InputBlackBoxOutput/NETHER/modules/HID module/firmware/src/connections.h

// AUX GPIO: Added for future extension and not used
// The ADC channel connected to pin 35 can be used to check LiPo battery voltage

#ifndef CONNECTIONS_H
#define CONNECTIONS_H

#define LED_S   16
#define LED_P   17

#define LED     22

#define AUX_1   23
#define AUX_2   25
#define AUX_3   26
#define AUX_4   27
#define AUX_5   32  // ADC
#define AUX_6   33  // ADC
#define AUX_7   34  // ADC
#define AUX_8   35  // ADC

#endif //CONNECTIONS_H
